ssfc59/dissertation/code/librarydisplayWORKING/arduino_secrets.h

//-------------WiFi settings-----------------------------
const char* ssid = "REPLACE-THIS-WITH-YOUR-WIFI-NAME";
const char* password = "REPLACE-THIS-WITH-YOUR-WIFI-PASSWORD";

//-------------API user settings--------------------------
const char* clientId = "REPLACE-WITH-YOUR-CLIENT-ID";
const char* clientSecret = "REPLACE-WITH-YOUR-CLIENT-SECRET";
const char* APIurl = "REPLACE-WITH-YOUR-API-URL";

//-----------Initial State user settings------------------
const char* accesskey = "REPLACE-WITH-YOUR-ACCESS-KEY";
const char* bucketkey = "REPLACE-WITH-YOUR-BUCKET-KEY";
